BoujeeEnjinia1701/wastewise-scan/cad/drawings/WSC-DWG-101.pdf

BUILD PLAN SKETCH, PLAN NOT YET BUILT WasteWise Scan · github.com/BoujeeEnjinia1701/wastewise-scan

FRONT VIEW
Scale 1:2; looking at the front (along +Y)

TOP VIEW
Scale 1:2; looking down (along -Z)

RIGHT VIEW
Scale 1:2; looking at the right side (along -X)

160

62 19

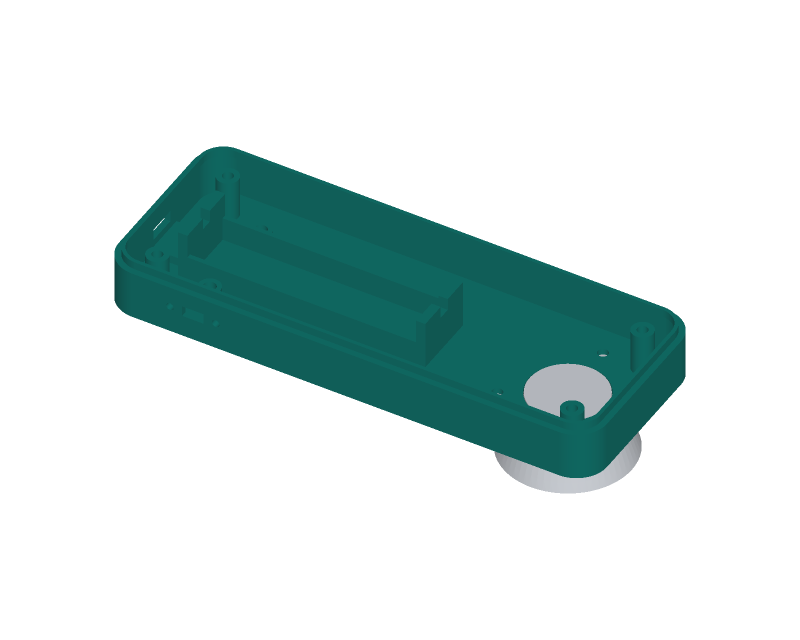
[picture p7: figure]

WHERE IT GOES
This part in colour, its neighbours in grey

HOW TO MAKE IT AND HOW IT FITS
Print open side up, 0.2 mm layers, 5 perimeters (2.0 mm walls), 40 % infill. Outside 160 x 62 x 16 mm, 10 mm corner radius; floor and walls 2.0 mm. Tongue 1.2 x 2.6 mm stands up inside the rim; it locates the top shell. Window hole 25.4 mm on the scan axis, 55 mm ahead of the centre. Three 3.4 mm holes round it on a 40 mm circle for the shroud screws. Four shell bosses 7 mm at 68 mm each side of centre, 20 mm out: 3.4 mm through, 6.2 mm counterbore 3.2 mm deep from below.
Cell cradle: two 1.5 mm rails and two 3 mm end walls 75 mm apart.
Two strap bosses beside the cradle take M3 inserts (4 mm hole).
Tail wall: USB-C opening 9.5 x 3.8 mm, 8 mm up; seat inside for the board. Right wall: switch slot 7 x 3.5 mm and two 2.4 mm holes 15 mm apart. Check: the top shell drops over the tongue without force.
REV | DESCRIPTION | DATE | BY
P1 | Making sketch for the prototype build plan | 2026-10-02 | AC
WASTEWISE SCAN | github.com/BoujeeEnjinia1701/wastewise-scan

## WasteWise Scan bottom shell: making sketch

DRAWING NO.
WSC-DWG-101

REV
P1

SHEET
1 of 1

SIZE

## ANSI B

SCALE
1:2

UNITS
mm
PROJECTION | DATE
2026-10-02

DRAWN
Amish Chadha

MATERIAL / NOTES
PETG, 3D printed
Licensed CERN-OHL-S-2.0 · Design Molecule Lab · designmolecule.com | Generated from cad/src; do not edit by hand
