BoujeeEnjinia1701/wastewise-scan/cad/drawings/WSC-DWG-102.pdf

BUILD PLAN SKETCH, PLAN NOT YET BUILT WasteWise Scan · github.com/BoujeeEnjinia1701/wastewise-scan

FRONT VIEW
Scale 1:2; looking at the front (along +Y)

TOP VIEW
Scale 1:2; looking down (along -Z)

RIGHT VIEW
Scale 1:2; looking at the right side (along -X)

160

64 18

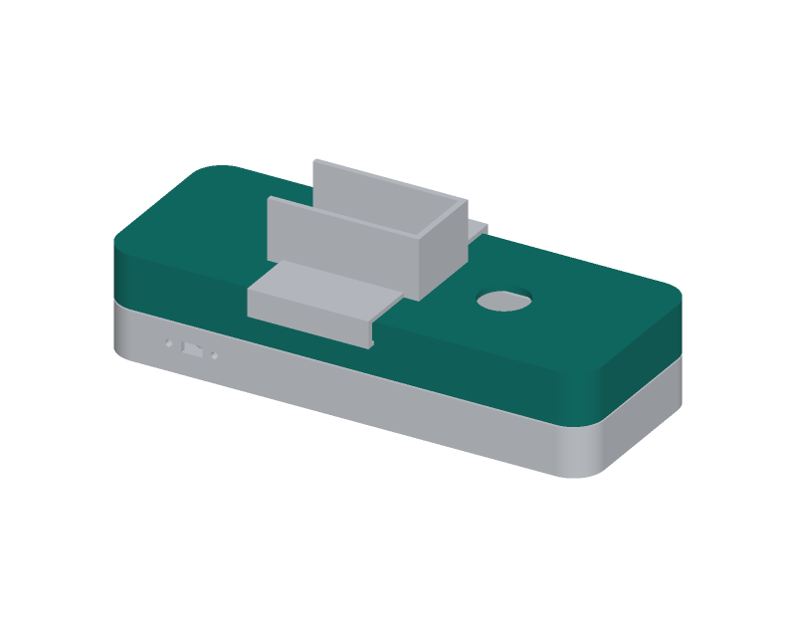
[picture p8: figure]

WHERE IT GOES
This part in colour, its neighbours in grey

HOW TO MAKE IT AND HOW IT FITS
Print upside down (top face on the bed), same settings as the bottom shell. Outside 160 x 62 x 17.4 mm; it sits on the gasket 16.6 mm up the body. Display window 46 x 24 mm centred 10 mm behind the body centre. Button hole 16.2 mm, 35 mm ahead of the body centre.
Four shell bosses reach down to meet the bottom shell bosses; they stop the gasket being squeezed below 0.6 mm. Press an M3 insert in each. Four frame bosses at 30 mm behind and 10 mm ahead of centre, 19 mm out each side; press an M3 insert in each.
Two clip ribs 36 x 1 x 1 mm on the outside of the side walls, 28 mm up the body; the sun hood legs snap under them.
Inserts: soldering iron at about 230 C, push square, flush with the boss. Check: each insert is square and flush; the ribs are unbroken.
REV | DESCRIPTION | DATE | BY
P1 | Making sketch for the prototype build plan | 2026-10-02 | AC
WASTEWISE SCAN | github.com/BoujeeEnjinia1701/wastewise-scan

## WasteWise Scan top shell: making sketch

DRAWING NO.
WSC-DWG-102

REV
P1

SHEET
1 of 1

SIZE

## ANSI B

SCALE
1:2

UNITS
mm
PROJECTION | DATE
2026-10-02

DRAWN
Amish Chadha

MATERIAL / NOTES
PETG, 3D printed
Licensed CERN-OHL-S-2.0 · Design Molecule Lab · designmolecule.com | Generated from cad/src; do not edit by hand
