BoujeeEnjinia1701/wastewise-scan/cad/drawings/WSC-DWG-104.pdf

BUILD PLAN SKETCH, PLAN NOT YET BUILT WasteWise Scan · github.com/BoujeeEnjinia1701/wastewise-scan

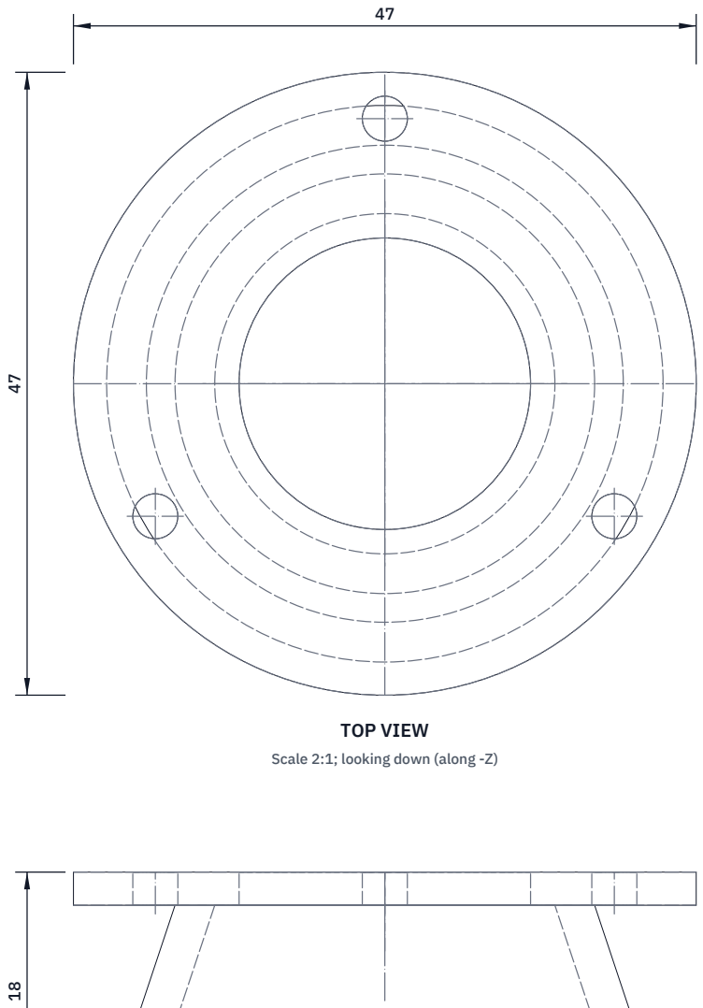
[picture p11: figure]
TOP VIEW; Scale 2:1; looking down (along -Z)

FRONT VIEW
Scale 2:1; looking at the front (along +Y)

RIGHT VIEW
Scale 2:1; looking at the right side (along -X)

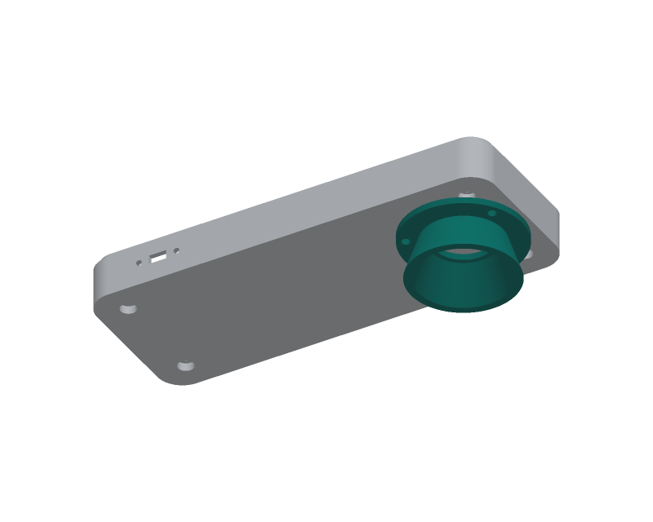
[picture p12: figure]

WHERE IT GOES
This part in colour, its neighbours in grey

HOW TO MAKE IT AND HOW IT FITS
Print in black TPU 95A, flange on the bed, slow (about 20 mm/s).
Flange 47 mm across and 2.5 mm thick, with a 22 mm hole; the lip of the flange holds the window up into the body.
Cone 18 mm deep from the body: 30 mm across at the flange, 42 mm at the rim, 3 mm wall; 36 mm inside at the rim.
Three 3.4 mm holes on a 40 mm circle, at 90, 210 and 330 degrees
(the first one toward the left side of the body).
Fit: three M3 x 10 screws with washers through the flange and the floor into the head block inserts. Snug only: TPU creeps if overtightened. The shroud wears; it is replaced with the same three screws.
Check: the rim sits flat on a sheet of glass with no light under it.
REV | DESCRIPTION | DATE | BY
P1 | Making sketch for the prototype build plan | 2026-10-02 | AC
WASTEWISE SCAN | github.com/BoujeeEnjinia1701/wastewise-scan

## WasteWise Scan light shroud: making sketch

DRAWING NO.
WSC-DWG-104

REV
P1

SHEET
1 of 1

SIZE

## ANSI B

SCALE
2:1

UNITS
mm
PROJECTION | DATE
2026-10-02

DRAWN
Amish Chadha

MATERIAL / NOTES
Black TPU 95A, 3D printed
Licensed CERN-OHL-S-2.0 · Design Molecule Lab · designmolecule.com | Generated from cad/src; do not edit by hand
