BoujeeEnjinia1701/wastewise-scan/cad/drawings/WSC-DWG-105.pdf

BUILD PLAN SKETCH, PLAN NOT YET BUILT WasteWise Scan · github.com/BoujeeEnjinia1701/wastewise-scan

FRONT VIEW
Scale 1:1; looking at the front (along +Y)

TOP VIEW
Scale 1:1; looking down (along -Z)

RIGHT VIEW
Scale 1:1; looking at the right side (along -X)

66

44 12

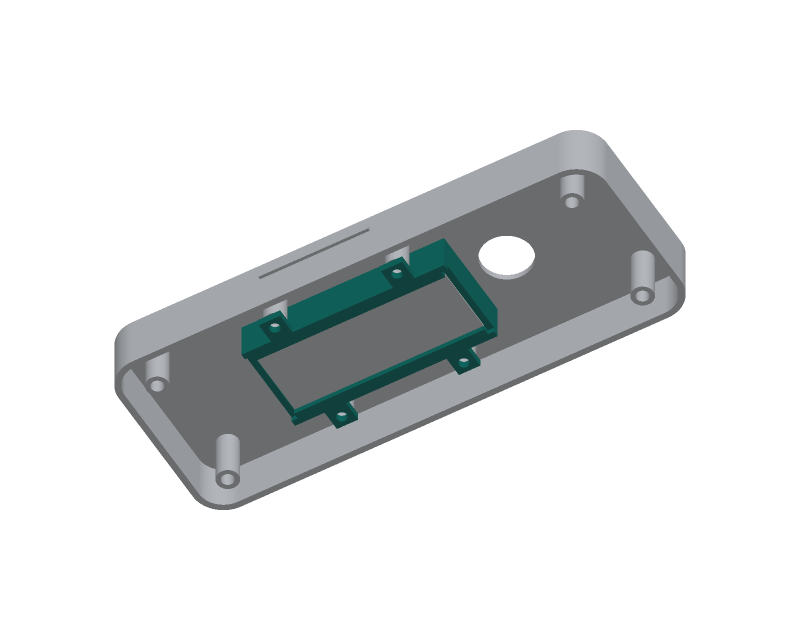
[picture p13: figure]

WHERE IT GOES
This part in colour, its neighbours in grey

HOW TO MAKE IT AND HOW IT FITS
Print with the lips and ears on the bed; the end walls bridge 26 mm. Inside 62.4 x 26.4 mm, walls 2 mm, 12 mm tall to the shell ceiling. Lips 2 mm wide under both long edges of the board, 1.75 mm thick. Four ears 7 x 7 x 2.5 mm with 3.4 mm holes, 19 mm each side of the centre line, 30 mm behind and 10 mm ahead of the body centre. Stick 0.5 mm foam tape on the lips so the board cannot rattle.
Fit: the display board drops in face up; the frame then goes into the upturned top shell with four M3 x 8 screws into the frame bosses. The screen sits 0.25 mm under the shell ceiling, behind the window. Check: the board drops in without force and the screen is centred.
REV | DESCRIPTION | DATE | BY
P1 | Making sketch for the prototype build plan | 2026-10-02 | AC
WASTEWISE SCAN | github.com/BoujeeEnjinia1701/wastewise-scan

## WasteWise Scan display frame: making sketch

DRAWING NO.
WSC-DWG-105

REV
P1

SHEET
1 of 1

SIZE

## ANSI B

SCALE
1:1

UNITS
mm
PROJECTION | DATE
2026-10-02

DRAWN
Amish Chadha

MATERIAL / NOTES
PETG, 3D printed
Licensed CERN-OHL-S-2.0 · Design Molecule Lab · designmolecule.com | Generated from cad/src; do not edit by hand
