BoujeeEnjinia1701/wastewise-scan/cad/drawings/WSC-DWG-106.pdf

BUILD PLAN SKETCH, PLAN NOT YET BUILT WasteWise Scan · github.com/BoujeeEnjinia1701/wastewise-scan

FRONT VIEW
Scale 2:1; looking at the front (along +Y)

TOP VIEW
Scale 2:1; looking down (along -Z)

RIGHT VIEW
Scale 2:1; looking at the right side (along -X)

10

33 23

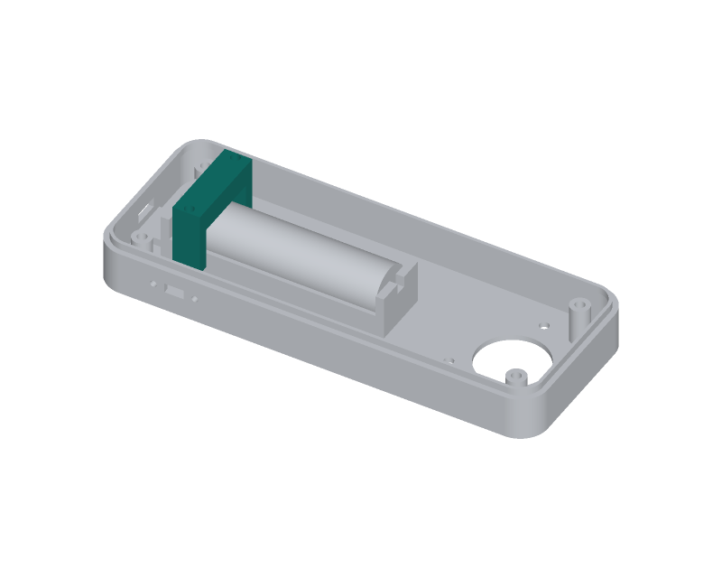
[picture p14: figure]

WHERE IT GOES
This part in colour, its neighbours in grey

HOW TO MAKE IT AND HOW IT FITS
Print on its side (the 10 mm face on the bed), 100 % infill.
A bridge 10 mm wide: top bar 33 x 8 mm, two legs 4 mm thick and 14.75 mm tall, 29 mm apart between centres.
3.4 mm hole down through each leg and the bar.
Fit: the bar lies on top of the cell, 46 mm from the cell's spring end; the legs stand on the two strap bosses beside the cradle.
Two M3 x 25 low-head screws down through the strap into the inserts. It holds the cell down in a drop: about 550 N at 1.3 times margin. Check: the cell cannot lift and the screw heads are below 31 mm.
REV | DESCRIPTION | DATE | BY
P1 | Making sketch for the prototype build plan | 2026-10-02 | AC
WASTEWISE SCAN | github.com/BoujeeEnjinia1701/wastewise-scan

## WasteWise Scan cell strap: making sketch

DRAWING NO.
WSC-DWG-106

REV
P1

SHEET
1 of 1

SIZE

## ANSI B

SCALE
2:1

UNITS
mm
PROJECTION | DATE
2026-10-02

DRAWN
Amish Chadha

MATERIAL / NOTES
PETG, 3D printed, 100 % infill
Licensed CERN-OHL-S-2.0 · Design Molecule Lab · designmolecule.com | Generated from cad/src; do not edit by hand
