BoujeeEnjinia1701/wastewise-scan/cad/drawings/WSC-DWG-107.pdf

BUILD PLAN SKETCH, PLAN NOT YET BUILT WasteWise Scan · github.com/BoujeeEnjinia1701/wastewise-scan

FRONT VIEW
Scale 1:1; looking at the front (along +Y)

TOP VIEW
Scale 1:1; looking down (along -Z)

RIGHT VIEW
Scale 1:1; looking at the right side (along -X)

50

68 28

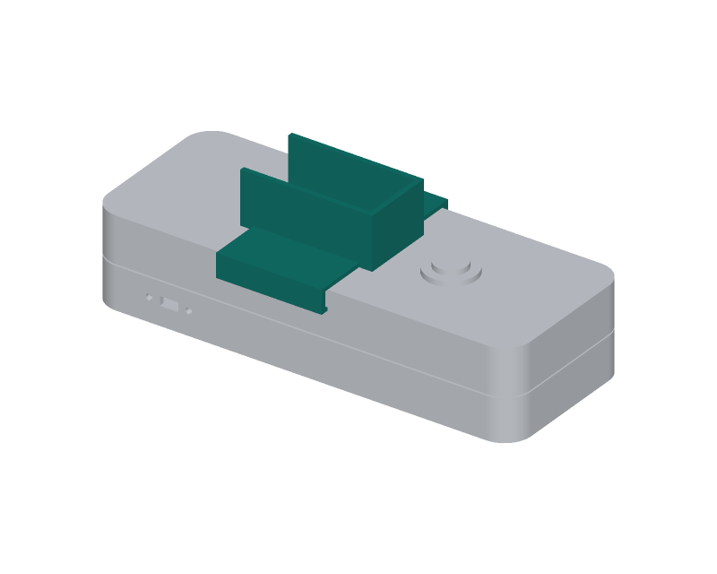
[picture p15: figure]

WHERE IT GOES
This part in colour, its neighbours in grey

HOW TO MAKE IT AND HOW IT FITS
Print upside down on the wall tops, with support under the plate. Plate 1.5 mm thick with the 46 x 24 mm display opening.
Walls 20 mm tall and 2 mm thick on both sides and the head end of the opening; the tail end is open toward the user.
Two clip legs 40 mm long, 2 mm thick, down both sides of the top shell; a lip on each leg snaps under the rib on the shell side.
Plate 68.4 mm across at the legs; legs 0.2 mm clear of the ribs.
Fit: press straight down until both lips click under the ribs. To take
it off, spread the legs with the thumbs and lift.
Check: it does not lift when the scanner is shaken face down.
REV | DESCRIPTION | DATE | BY
P1 | Making sketch for the prototype build plan | 2026-10-02 | AC
WASTEWISE SCAN | github.com/BoujeeEnjinia1701/wastewise-scan

## WasteWise Scan sun hood: making sketch

DRAWING NO.
WSC-DWG-107

REV
P1

SHEET
1 of 1

SIZE

## ANSI B

SCALE
1:1

UNITS
mm
PROJECTION | DATE
2026-10-02

DRAWN
Amish Chadha

MATERIAL / NOTES
PETG, 3D printed
Licensed CERN-OHL-S-2.0 · Design Molecule Lab · designmolecule.com | Generated from cad/src; do not edit by hand
