BoujeeEnjinia1701/wastewise-scan/cad/drawings/WSC-DWG-108.pdf

BUILD PLAN SKETCH, PLAN NOT YET BUILT WasteWise Scan · github.com/BoujeeEnjinia1701/wastewise-scan

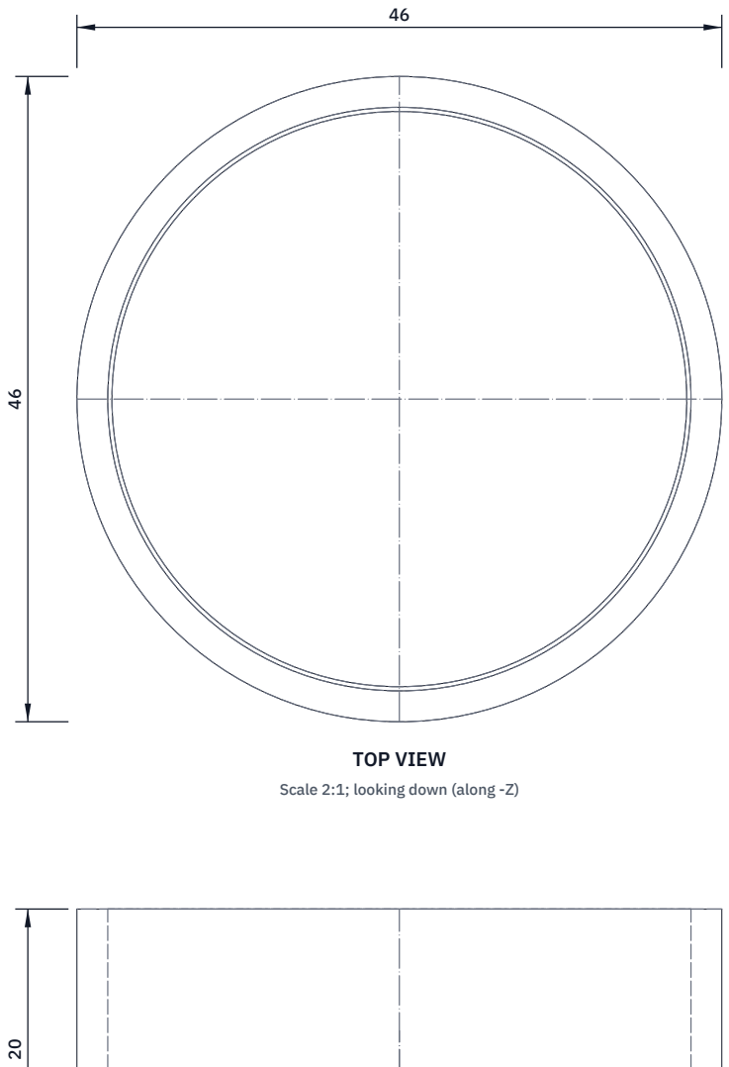
[picture p16: figure]
TOP VIEW; Scale 2:1; looking down (along -Z)

FRONT VIEW
Scale 2:1; looking at the front (along +Y)

RIGHT VIEW
Scale 2:1; looking at the right side (along -X)

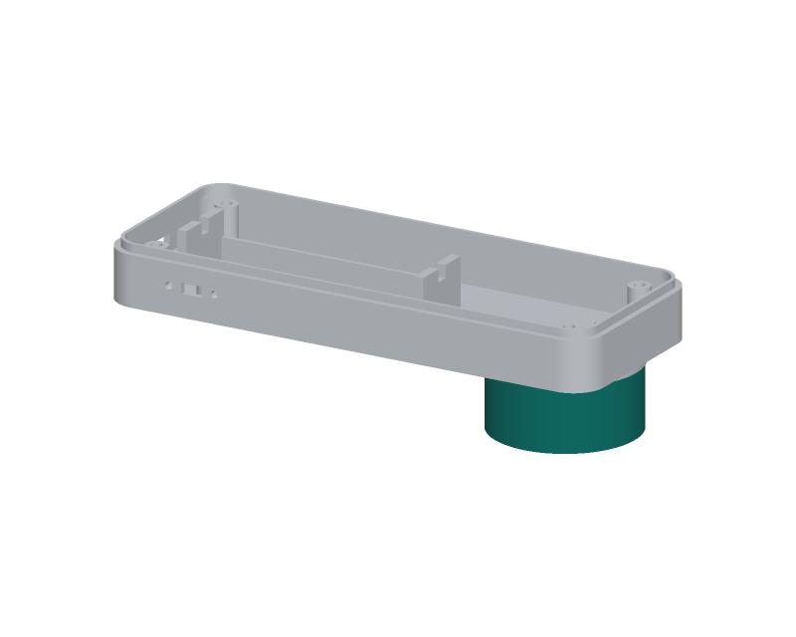
[picture p17: figure]

WHERE IT GOES
This part in colour, its neighbours in grey

HOW TO MAKE IT AND HOW IT FITS
Cap: print open end up in black PETG, 100 % infill so no light passes. 46 mm across, 20 mm tall, floor 2 mm, bore 41.6 mm.
Disc: cut 41 mm from 3 mm white PTFE sheet with a knife and file; sand the top face matte with 400 grit; do not touch it after.
Press the disc into the cap, sanded face up; a drop of glue at the edge. Fit: the cap pushes over the shroud; the bore grips the 42 mm rim and the rim rests on the disc, as it rests on an item when scanning.
The cap mouth stops 0.5 mm below the shroud flange.
Check: pushed fully on, the rim touches the disc all round.
REV | DESCRIPTION | DATE | BY
P1 | Making sketch for the prototype build plan | 2026-10-02 | AC
WASTEWISE SCAN | github.com/BoujeeEnjinia1701/wastewise-scan

## WasteWise Scan calibration cap and PTFE disc: making sketch

DRAWING NO.
WSC-DWG-108

REV
P1

SHEET
1 of 1

SIZE

## ANSI B

SCALE
2:1

UNITS
mm
PROJECTION | DATE
2026-10-02

DRAWN
Amish Chadha

MATERIAL / NOTES
Black PETG cap, 3D printed; PTFE sheet 3 mm
Licensed CERN-OHL-S-2.0 · Design Molecule Lab · designmolecule.com | Generated from cad/src; do not edit by hand
