BoujeeEnjinia1701/wastewise-scan/cad/drawings/WSC-DWG-109.pdf

BUILD PLAN SKETCH, PLAN NOT YET BUILT WasteWise Scan · github.com/BoujeeEnjinia1701/wastewise-scan

FRONT VIEW
Scale 2:1; looking at the front (along +Y)

TOP VIEW
Scale 2:1; looking down (along -Z)

RIGHT VIEW
Scale 2:1; looking at the right side (along -X)

28

28 2

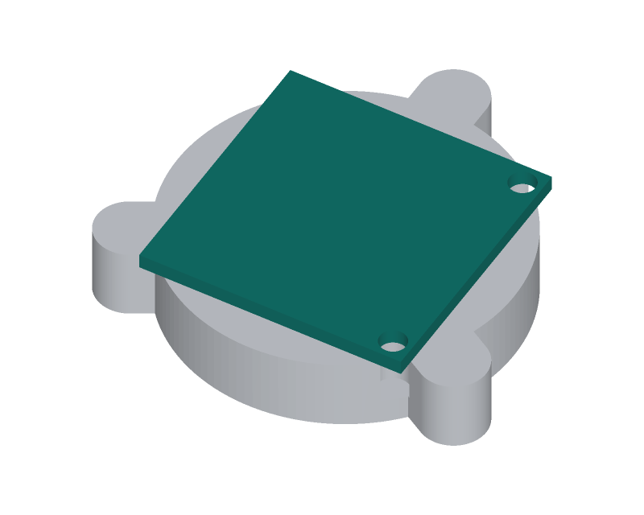
[picture p18: figure]

WHERE IT GOES
This part in colour, its neighbours in grey

HOW TO MAKE IT AND HOW IT FITS
Cut 28 x 28 mm of perfboard; file the edges square.
Drill two 2.8 mm holes 12 mm from the scan axis toward the head end, 12 mm each side, for M2.5 x 6 screws into the head block.
Hold the board on the head block with the LEDs and photodiode in their pockets and mark where every lead comes through; open those holes. Build the amplifier, the 24-bit converter and the LED switches on the
top face as the wiring picture shows; keep the photodiode input short. The LED switches include a hardware limit on how long an LED can stay on. Check: every lead passes through without bending the LED or photodiode.
REV | DESCRIPTION | DATE | BY
P1 | Making sketch for the prototype build plan | 2026-10-02 | AC
WASTEWISE SCAN | github.com/BoujeeEnjinia1701/wastewise-scan

## WasteWise Scan amplifier board: making sketch

DRAWING NO.
WSC-DWG-109

REV
P1

SHEET
1 of 1

SIZE

## ANSI B

SCALE
2:1

UNITS
mm
PROJECTION | DATE
2026-10-02

DRAWN
Amish Chadha

MATERIAL / NOTES
Perfboard, 2.54 mm pitch, 1.6 mm
Licensed CERN-OHL-S-2.0 · Design Molecule Lab · designmolecule.com | Generated from cad/src; do not edit by hand
