BoujeeEnjinia1701/wastewise-scan/cad/drawings/WSC-DWG-001.png

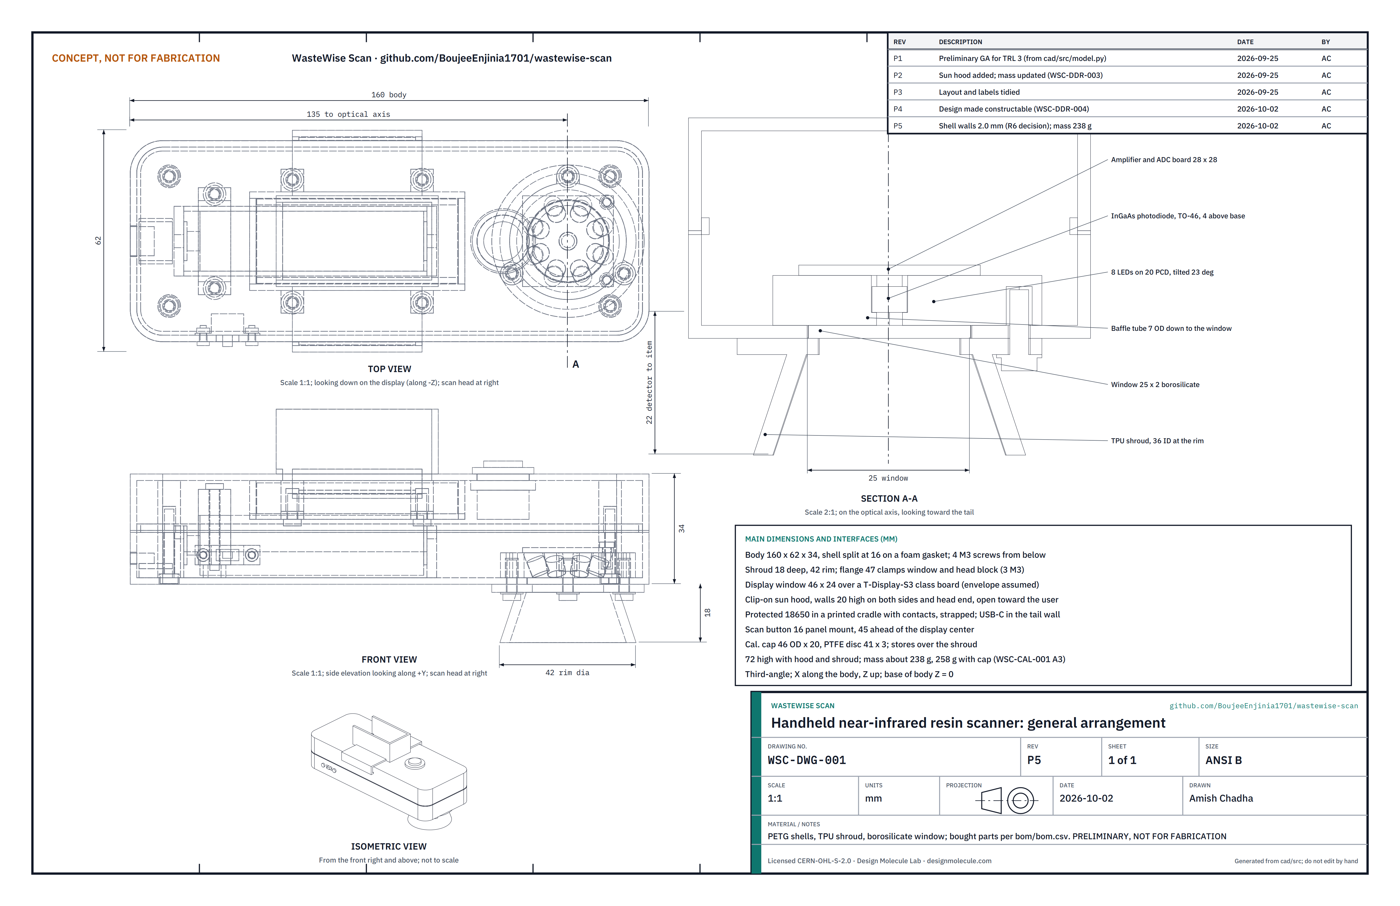
cad/drawings/WSC-DWG-001.png
