BoujeeEnjinia1701/wastewise-scan/media/card.png

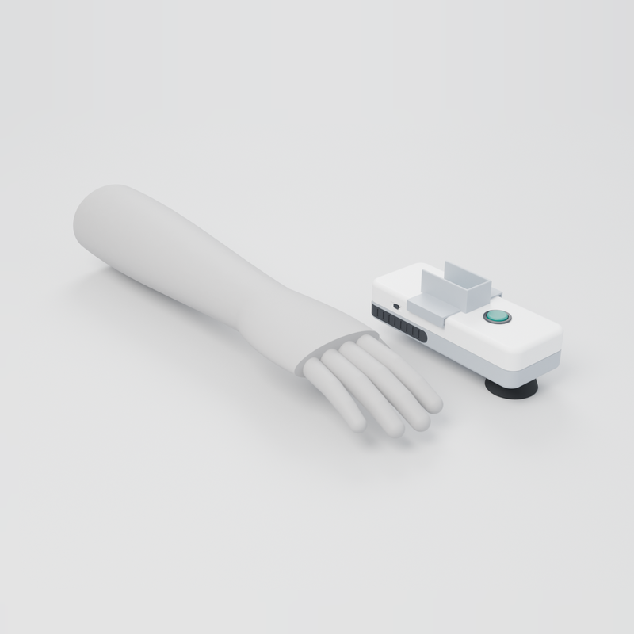
media/card.png
