BoujeeEnjinia1701/wastewise-scan/media/render-detail.png

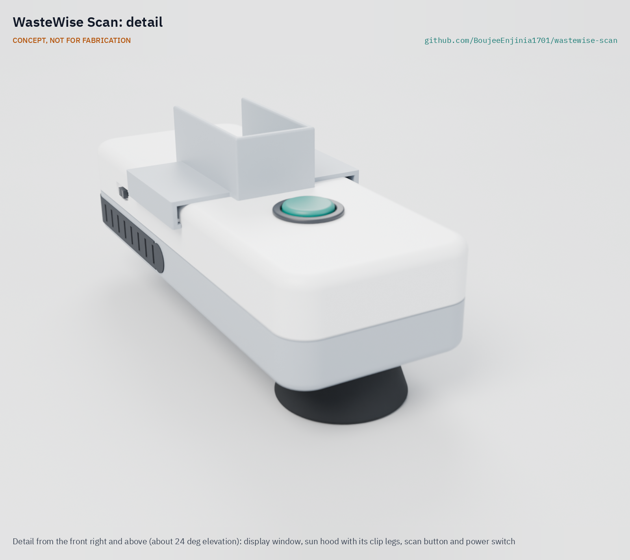
media/render-detail.png
