BoujeeEnjinia1701/wastewise-scan/media/render-exploded.png

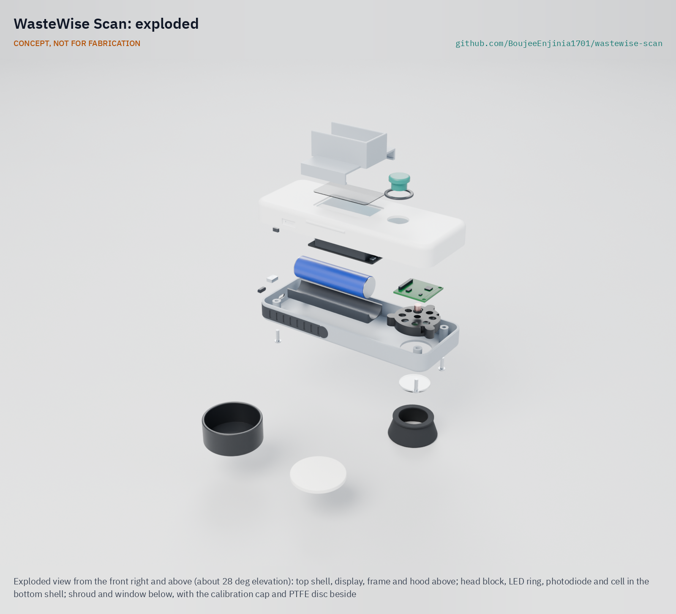
media/render-exploded.png
