BoujeeEnjinia1701/wastewise-scan/media/render-hero-plain.png

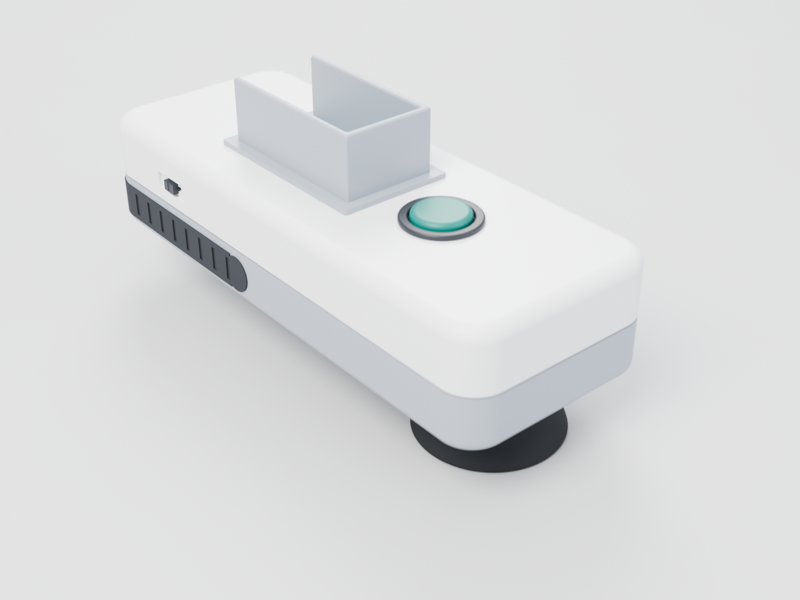
media/render-hero-plain.png
