BoujeeEnjinia1701/wastewise-scan/media/social-preview.png

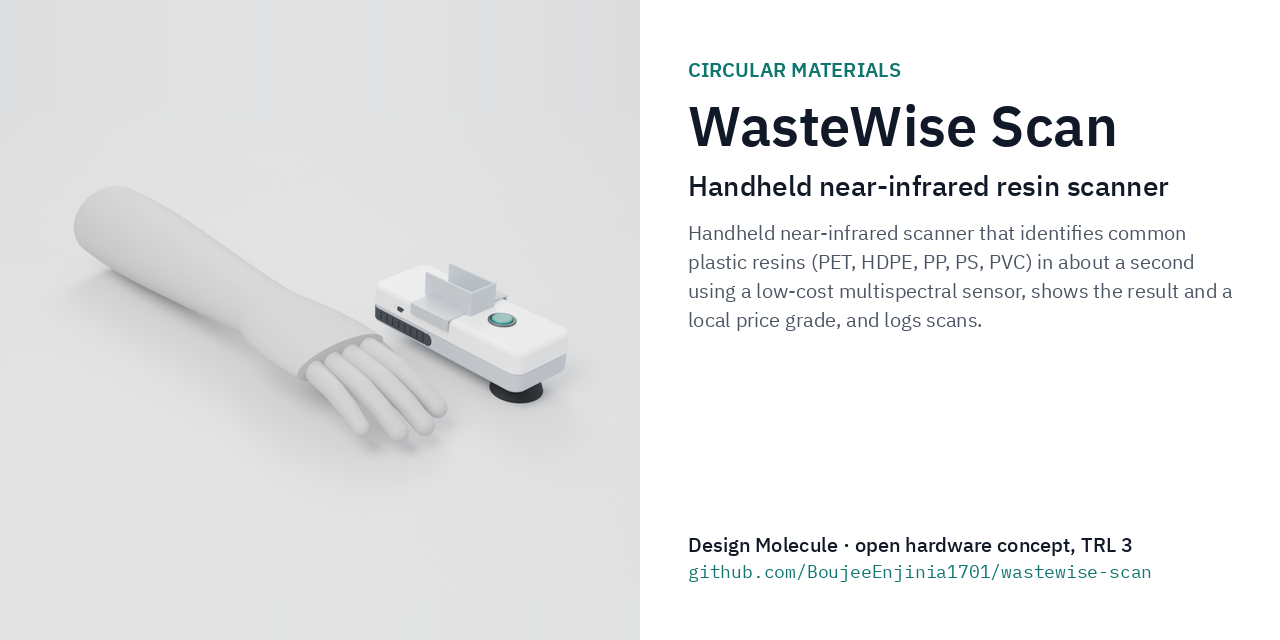
media/social-preview.png
